akreager/cd_changer_emulator/docs/TL-KRC3006-02.odt

Field | Value
Document Number | TL-KRC3006-02
Companion Test Plan | TP-KRC3006-02
Revision | B
Date | 2026-03-29
Board Serial / ID
Tester

Record all test results in the tables below. Write PASS or FAIL in the Result column. For any FAIL result, record details in the Notes column including the measured value and the nature of the failure. Attach photographs of defects where practical.

Phase 1 — Bare Board Inspection and Testing

Visual Inspection

Step | Description | Result | Notes
1.1 | Board outline and dimensions (22 x 80 mm +/- 0.2 mm)
1.2 | Remove edge burrs
1.3 | Audio jack cutout geometry
1.4 | Through-holes (J1, J2, J3, J4, J5)
1.5 | Front copper traces (F.Cu)
1.6 | Back copper traces (B.Cu)
1.7 | Front silkscreen legibility and correctness
1.8 | Back silkscreen legibility and correctness
1.9 | Solder mask coverage and alignment

Bare Board Electrical — Pass-Through Continuity (J1 to J2)

DMM continuity mode. Measure pad-to-pad on bare board. Accept: < 1 ohm.

Step | DIN Pin | Signal | Measured | Result | Notes
1.10a | 1 | REQ H
1.10b | 2 | GND
1.10c | 3 | B.U.
1.10d | 4 | ON
1.10e | 5 | MUTE
1.10f | 6 | D. GND
1.10g | 7 | RESET
1.10h | 9 | REQ C
1.10i | 10 | DATA C
1.10j | 11 | DATA H
1.10k | 13 | CLK

Bare Board Electrical — J3 Test Header Continuity (J1 to J3)

DMM continuity mode. Measure J3 pad to corresponding J1 pad. Accept: < 1 ohm.

Step | J3 Pin | Signal | Measured | Result | Notes
1.11a | 1 | GND
1.11b | 2 | ON
1.11c | 3 | B.U.
1.11d | 4 | RESET
1.11e | 5 | D. GND
1.11f | 6 | REQ H
1.11g | 7 | REQ C
1.11h | 8 | MUTE
1.11i | 9 | DATA C
1.11j | 10 | DATA H
1.11k | 11 | CLK

Bare Board Electrical — Audio Path Continuity

DMM continuity mode. Accept: < 1 ohm.

Step | From | To | Measured | Result | Notes
1.12a | J1 Pin 8 (R CH) | J4 Tip pad
1.12b | J1 Pin 12 (L CH) | J4 Ring pad
1.12c | J1 Pin 2 (GND) | J4 Sleeve pad
1.13a | J2 Pin 8 (R CH) | J5 Tip pad
1.13b | J2 Pin 12 (L CH) | J5 Ring pad
1.13c | J2 Pin 2 (GND) | J5 Sleeve pad

Bare Board Electrical — Isolation

DMM resistance mode. Accept: > 1 M ohm (open circuit).

Step | Between | And | Measured | Result | Notes
1.14a | J4 Tip pad | J5 Tip pad
1.14b | J4 Ring pad | J5 Ring pad
1.15a | B.U. (Pin 3) | GND (Pin 2)
1.15b | B.U. (Pin 3) | ON (Pin 4)
1.15c | B.U. (J3 Pin 3) | J3 Pin 2 (adjacent)
1.15d | B.U. (J3 Pin 3) | J3 Pin 4 (adjacent)
1.16a | Spot check 1:
1.16b | Spot check 2:
1.16c | Spot check 3:
1.16d | Spot check 4:
1.16e | Spot check 5:

Phase 1 Result

Phase 1 Overall Result | Date | Tester Initials | Notes

Phase 2 — Assembly and Workmanship

Workmanship Inspection

Step | Description | Result | Notes
2.1 | J3 solder joints (11 pins)
2.2 | J4 and J5 solder joints and seating
2.3 | J1 solder joints (13 signal pins + lugs)
2.4 | J2 solder joints (back side, 13 signal pins + lugs)
2.5 | Post-solder cleaning (flux removal)
2.6 | Final visual inspection

Phase 2 Result

Phase 2 Overall Result | Date | Tester Initials | Notes

Phase 3 — Final Electrical Verification

End-to-End Continuity

DMM continuity mode. Measure with connectors/cables inserted. Accept: < 2 ohm.

Step | Path | Measured | Result | Notes
3.1a | Cable Pin 1 (REQ H) through J1-J2 to J2 Pin 1
3.1b | Cable Pin 2 (GND) through J1-J2 to J2 Pin 2
3.1c | Cable Pin 3 (B.U.) through J1-J2 to J2 Pin 3
3.1d | Cable Pin 4 (ON) through J1-J2 to J2 Pin 4
3.1e | Cable Pin 5 (MUTE) through J1-J2 to J2 Pin 5
3.1f | Cable Pin 6 (D. GND) through J1-J2 to J2 Pin 6
3.1g | Cable Pin 7 (RESET) through J1-J2 to J2 Pin 7
3.1h | Cable Pin 9 (REQ C) through J1-J2 to J2 Pin 9
3.1i | Cable Pin 10 (DATA C) through J1-J2 to J2 Pin 10
3.1j | Cable Pin 11 (DATA H) through J1-J2 to J2 Pin 11
3.1k | Cable Pin 13 (CLK) through J1-J2 to J2 Pin 13

J3 Test Header End-to-End

With cable in J1, insert jumper wire into each J3 socket. Accept: < 2 ohm.

Step | J3 Pin / Signal | Measured | Result | Notes
3.2a | J3:1 -> J1:2
3.2b | J3:2 -> J1:4
3.2c | J3:3 -> J1:3
3.2d | J3:4 -> J1:7
3.2e | J3:5 -> J1:6
3.2f | J3:6 -> J1:1
3.2g | J3:7 -> J1:9
3.2h | J3:8 -> J1:5
3.2i | J3:9 -> J1:10
3.2j | J3:10 -> J1:11
3.2k | J3:11 -> J1:13

Audio Path End-to-End

With cables in J1/J2 and 3.5 mm plugs in J4/J5. Accept: < 2 ohm.

Step | Path | Measured | Result | Notes
3.3a | J1:8 -> J4:Tip (R CH)
3.3b | J1:12 -> J4:Ring (L CH)
3.3c | J1:2 -> J4:Sleeve (GND)
3.4a | J2:8 -> J5:Tip (R CH)
3.4b | J2:12 -> J5:Ring (L CH)
3.4c | J2:2 -> J5:Sleeve (GND)

Audio Isolation and Jumper Verification

Step | Test | Measured | Result | Notes
3.5a | J4 Tip to J5 Tip — NO cable (expect open)
3.5b | J4 Ring to J5 Ring — NO cable (expect open)
3.5c | J4 Tip to J5 Tip — WITH 3.5mm cable (expect < 2 ohm)
3.5d | J4 Ring to J5 Ring — WITH 3.5mm cable (expect < 2 ohm)

Phase 3 Result

Phase 3 Overall Result | Date | Tester Initials | Notes

Final Acceptance

| Result | Date | Initials
Phase 1 — Bare Board
Phase 2 — Assembly
Phase 3 — Final Verification
BOARD ACCEPTED FOR TP-KRC3006-01

Defect Log (attach additional pages if needed):

Defect # | Step | Description | Disposition (rework / accept / scrap) | Verified By
1
2
3
4
5

Revision History

Rev | Date | Author | Description
A | 2026-03-14 | Allen | Initial release.
B | 2026-03-29 | A. Kreager | Add step to remove burrs
C | 2026-04-01 | A. Kreager | Formatting. Corrected 1.11 signal names.

TL-KRC3006-02 Breakout Board Test Log
