akreager/cd_changer_emulator/docs/records/TL-KRC3006-01-P1-20260419.pdf

### TL-KRC3006-01 Rev B

Project: | Kenwood C
Date:
Tester:
Equipment / Component | Ref ID | Description / Model | Serial Number | Cal Due Date | Notes
Kenwood KRC-3006 | KEN-01 | Head unit (DUT)
Kenwood KDC-C717 | KEN-02 | CD changer
Bench Power Supply | PWR-01
Staged Power Adapter | PWR-02 | Custom 2-stage ignition sim.
KRC-3006 DC Cord | PWR-03 | Power/speaker harness
USB Logic Analyzer | LA-01 | SparkFun TOL-18627 or equiv.
Digital Multimeter | DMM-01
13-Pin DIN Cable | CBL-01 | Kenwood changer cable
13-Pin Breakout Board | MOD-02 | Prototyping board
Pass-Through Board | MOD-03 | DN-KRC3006-04 custom PCB
PulseView (sigrok) | SW-01 | Logic analyzer software

Phase 1 — Static Verification

## TL-KRC3006-01 Rev B

Project: | Kenwood CD Changer Protocol Emulator (Open Source)
Date: | 2026-04-19
Tester: | A. KREAGER

Initial Power-Up
Step | Action | Expected | Result | P/F | Date | Notes
2 | PSU on, constant power on | PSU stable at 12.0 V | | PASS | 2026-04-19 | INITIAL INRUSH PEAKED AT .1A. SETTLED AT .003A
3 | Ignition power on | Head unit powers on | | PASS | 2026-04-19 | RADIO IS INITTIAL SOURCE, .4A PLAYING STATIC AT LOW VOLUME
4 | Idle current draw | 0.5–1.5 A | .49V | PASS | 2026-04-19
5 | Select CD-CH source | Error/search display | E01 | PASS | 2026-04-19 | NO MAGAZINE LOADED. LOADS AND PLAYS DISC UPON INSERTION

13-Pin DIN Voltage Measurements
Pin | Signal | Function | Dir | Expected V | Measured V | Notes
1 | CH-REQH | Request (H→C) | Out | Logic HIGH idle | 4.88
2 | GND | Digital Ground | — | 0 V (ref) | 0 | 7.5 OHM
3 | +12V | Power Supply | Out | 11.5–12.5 V | 11.97
4 | CH-CON | Changer Connect | Out | Toggle w/ source | 4 | LINE GOES HIGH WHEN CHANGER IS SELECTED
5 | CH-MUTE | Mute Request | In | Logic HIGH idle | 0 3.5 | IDLE LOW LOGIC HIGH ENABLE
6 | AGND | Audio Ground | — | 0 V / isolated | | REFERENCE
7 | CH-RST | Reset | Out | Logic HIGH idle | 0 4 | IDLE LOW LOGIC HIGH ENABLE
8 | R-CH | Right Audio | In | 0 V (no source) | | NOT TESTED
9 | CH-REQC | Request (C→H) | In | Logic HIGH idle | 5.04
10 | CH-DATAC | Data (C→H) | In | Logic LOW idle | 5.11
11 | CH-DATAH | Data (H→C) | Out | Logic LOW idle | 0 4.87 | IDLE LOW LOGIC HIGH WHILE PLAYING DISC
12 | L-CH | Left Audio | In | 0 V (no source) | | NOT TESTED
13 | CLK | Clock | Out | Toggling / 0 V | 5.15 | IDLE 0HZ DISC PLAYING 31.6 HZ TRACK CHANGE ~100HZ, DROP TO ~8HZ, BACK TO ~32HZ

Ground Continuity
Test | Expected | Result | P/F | Date | Tester | Notes
Pin 2 ↔ Pin 6 | Continuity or isolated | CONTINUITY | | 2026-04-19 | AK

Phase 1 Overall Result:

Phase 2A — Idle Capture

## TL-KR

Project:Kenwood CD Changer Pro Date:
Tester:
Capture # Clock Freq (kHz) | Polling Interval | CLK Behavior REQH Behavior P/F | Notes
Capture # | Total Bits | Decoded Hex (H→C) Header BytesCommand ByteData BytesNotes / Comparison to Mictronics
File Name | Date/Time | Duration (s) | Sample RateDescription | P/F | Notes

Phase 2

Phase 2B — Changer Capture

## TL-KR

Project:Kenwood CD Changer Date:
Tester:
Check | Expected | Observed | P/F | Date | Tester | Notes
BreakoutConnected

MagazinDisc in slot 1

No shorAll clear

Capture # | Hex (H→C) | Hex (C→H) | Handshake DetailCH-CON State CH-MUTE State | Notes
Capture # | Hex (H→C) | Hex (C→H) | Disc # | Track # | State | Notes
File Name | Date/Time | Duration (s) | Sample Rate | Description | P/F | Notes

Phase 2

Phase 3 — Command Map
TL-KRC3006-0
Project: | Kenwood C
Date:
Tester:

Command Mapping
Button / Action Capture #Cmd Hex (H→C) Response Hex (C→H) State Change Matches Mictronics? | Notes
Play

Pause

Next Track

Previous Track

Fast Forward (hold)

Fast Reverse (hold)

Disc Up

Disc Down

Disc Select 1

Disc Select 2

Disc Select 3

Disc Select 4

Disc Select 5

Disc Select 6

Repeat Toggle

Random/Shuffle Togg

Next Track (last track

Prev Track (track 1)

Disc Up (last disc)

Disc Select (empty sl

Capture File Log
File Name | Date/Time Duration (s) | Sample Rate | Description | P/F | Notes

Phase 3 Overall Res

Incidents

## TL-KR

Project:Kenwood CD
Date:
Tester:
Inc # | Severity | Phase/Step | Expected | Observed | Date | Root Cause | Resolution

Severit
Critical Head unit d
Major Protocol co
Minor Specific co
ObservaBehavior dif
Inc # | Severity | Phase/Step | Expected | Observed | Date | Root Cause | Resolution
